morisobaR/BitDeck10/doc/image/back.jpg

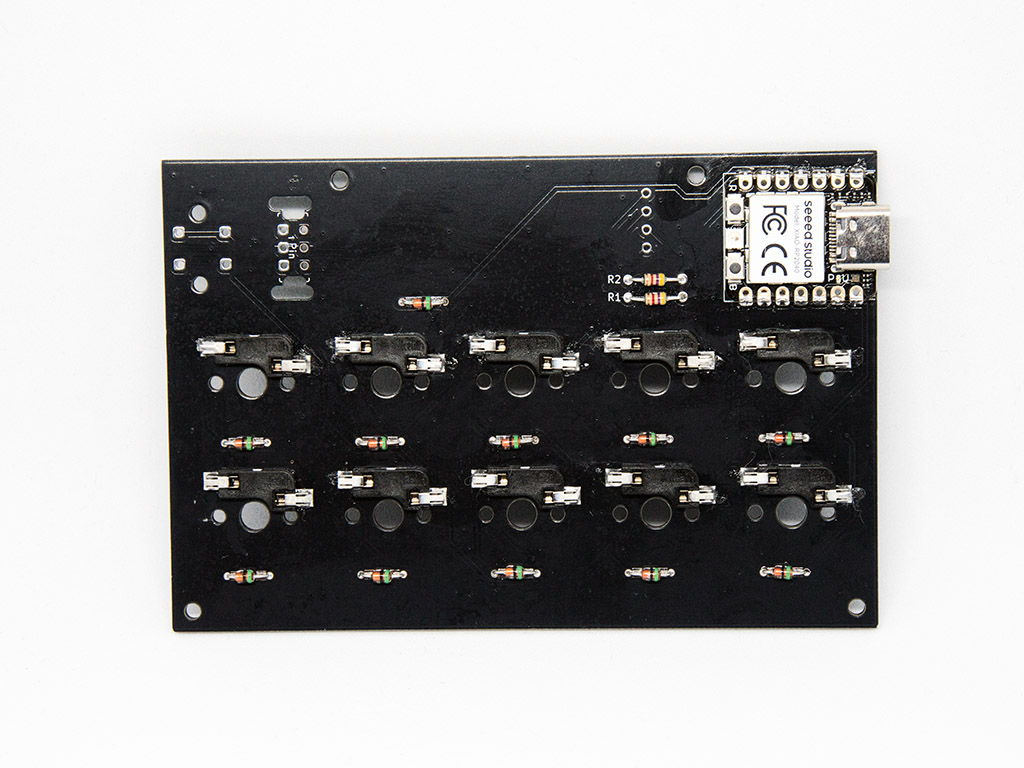
doc/image/back.jpg
